kevinfodor/wake-on-sleep/code/pic/wake_on_sleep.X/configuration_bits.c

/******************************************************************************/
/* Files to Include                                                           */
/******************************************************************************/

#if defined(__XC)
#include <xc.h>         /* XC8 General Include File */
#elif defined(HI_TECH_C)
#include <htc.h>        /* HiTech General Include File */
#elif defined(__18CXX)
#include <p18cxxx.h>    /* C18 General Include File */
#endif

#if defined(__XC) || defined(HI_TECH_C) || defined (__MINGW32__)

#include <stdint.h>        /* For uint8_t definition */
#include <stdbool.h>       /* For true/false definition */

#endif

/******************************************************************************/
/* Configuration Bits                                                         */
/*                                                                            */
/* Refer to 'HI-TECH PICC and PICC18 Toolchains > PICC18 Configuration        */
/* Settings' under Help > Contents in MPLAB X IDE for available PIC18         */
/* Configuration Bit Settings for the correct macros when using the C18       */
/* compiler.  When using the Hi-Tech PICC18 compiler, refer to the compiler   */
/* manual.pdf in the compiler installation doc directory section on           */
/* 'Configuration Fuses'.  The device header file in the HiTech PICC18        */
/* compiler installation directory contains the available macros to be        */
/* embedded.  The XC8 compiler contains documentation on the configuration    */
/* bit macros within the compiler installation /docs folder in a file called  */
/* pic18_chipinfo.html.                                                       */
/*                                                                            */
/* For additional information about what the hardware configurations mean in  */
/* terms of device operation, refer to the device datasheet.                  */
/*                                                                            */
/* General C18/XC8 syntax for configuration macros:                           */
/* #pragma config <Macro Name>=<Setting>, <Macro Name>=<Setting>, ...         */
/*                                                                            */
/* General HiTech PICC18 syntax:                                              */
/* __CONFIG(n,x);                                                             */
/*                                                                            */
/* n is the config word number and x represents the anded macros from the     */
/* device header file in the PICC18 compiler installation include directory.  */
/*                                                                            */
/* A feature of MPLAB X is the 'Generate Source Code to Output' utility in    */
/* the Configuration Bits window.  Under Window > PIC Memory Views >          */
/* Configuration Bits, a user controllable configuration bits window is       */
/* available to Generate Configuration Bits source code which the user can    */
/* paste into this project.                                                   */
/*                                                                            */
/******************************************************************************/

#if (__18F45K20 == 1) || (_18F45K20 == 1)

#pragma config FOSC = INTIO67, FCMEN = OFF, IESO = OFF                      // CONFIG1H
#pragma config PWRT = OFF, BOREN = OFF, BORV = 30                           // CONFIG2L
#pragma config WDTEN = OFF, WDTPS = 32768                                   // CONFIG2H
#pragma config MCLRE = ON, LPT1OSC = OFF, PBADEN = OFF, CCP2MX = PORTC      // CONFIG3H
#pragma config STVREN = ON, LVP = OFF, XINST = OFF                          // CONFIG4L
#pragma config CP0 = OFF, CP1 = OFF, CP2 = OFF, CP3 = OFF                   // CONFIG5L
#pragma config CPB = OFF, CPD = OFF                                         // CONFIG5H
#pragma config WRT0 = OFF, WRT1 = OFF, WRT2 = OFF, WRT3 = OFF               // CONFIG6L
#pragma config WRTB = OFF, WRTC = OFF, WRTD = OFF                           // CONFIG6H
#pragma config EBTR0 = OFF, EBTR1 = OFF, EBTR2 = OFF, EBTR3 = OFF           // CONFIG7L
#pragma config EBTRB = OFF                                                  // CONFIG7H

#elif (__16F1823 == 1) || (_16F1823 == 1)

// CONFIG1
#pragma config CPD = OFF, BOREN = OFF, IESO = OFF, FOSC = INTOSC
#pragma config FCMEN = OFF, MCLRE = ON, WDTE = OFF, CP = OFF, PWRTE = OFF
#pragma config CLKOUTEN = OFF

// CONFIG2
#pragma config PLLEN = OFF, WRT = OFF, STVREN = OFF, BORV = LO, LVP = OFF

#elif __MINGW32__

// Nothing to configure

#else

#error Error! You must create definitions for this processor.

#endif
